VaAndCob/PrintpooP/squareline/assets/puppy/stage0.png

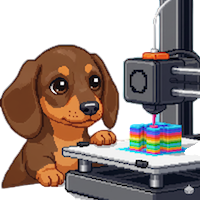
squareline/assets/puppy/stage0.png
