VaAndCob/PrintpooP/squareline/assets/puppy/stage1.png

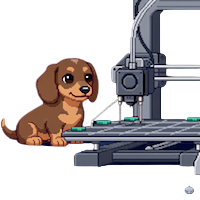
squareline/assets/puppy/stage1.png
