VaAndCob/PrintpooP/squareline/assets/puppy/stage2.png

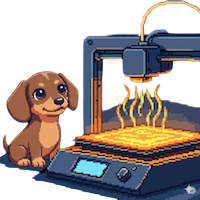
squareline/assets/puppy/stage2.png
