VaAndCob/PrintpooP/squareline/assets/puppy/stage4.png

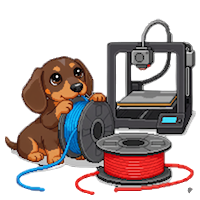
squareline/assets/puppy/stage4.png
