VaAndCob/PrintpooP/squareline/assets/puppy/stage8.png

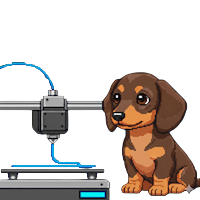
squareline/assets/puppy/stage8.png
