VaAndCob/PrintpooP/squareline/assets/puppy/stage13.png

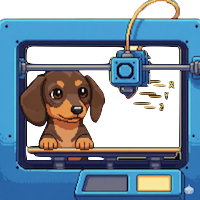
squareline/assets/puppy/stage13.png
