VaAndCob/PrintpooP/squareline/assets/puppy/stage24.png

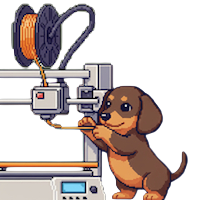
squareline/assets/puppy/stage24.png
