VaAndCob/PrintpooP/squareline/assets/puppy/stage_1.png

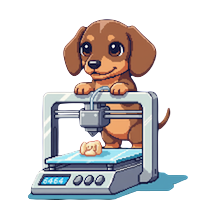
squareline/assets/puppy/stage_1.png
