VaAndCob/PrintpooP/3dprint/printpoop1.jpg

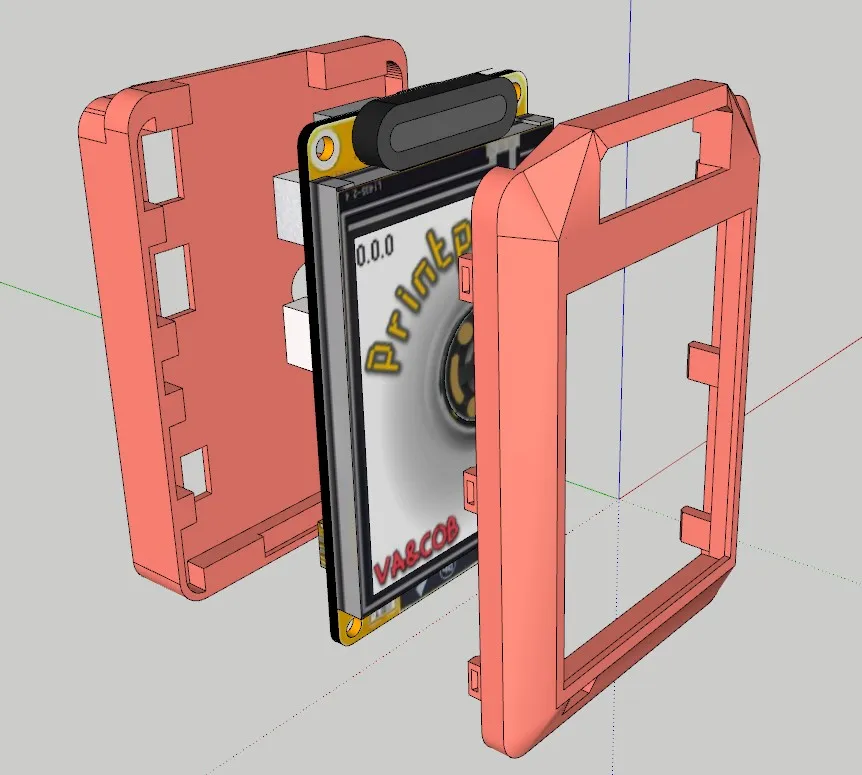
3dprint/printpoop1.jpg
