VaAndCob/PrintpooP/3dprint/printpoop2.jpg

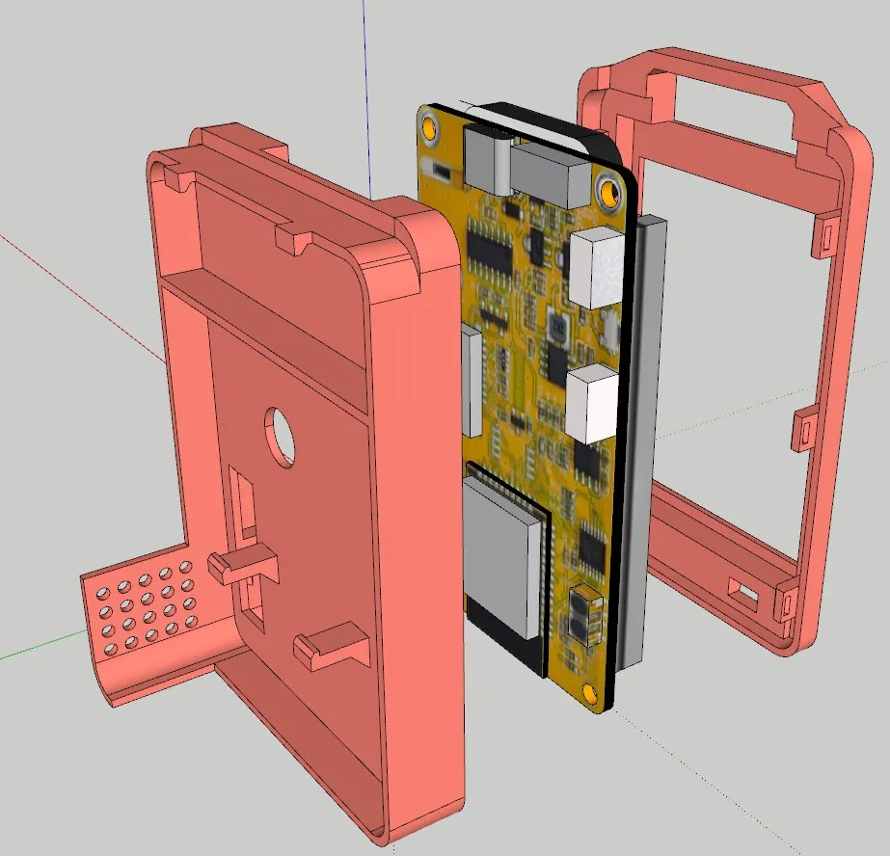
3dprint/printpoop2.jpg
