VaAndCob/PrintpooP/3dprint/printpoop3.jpg

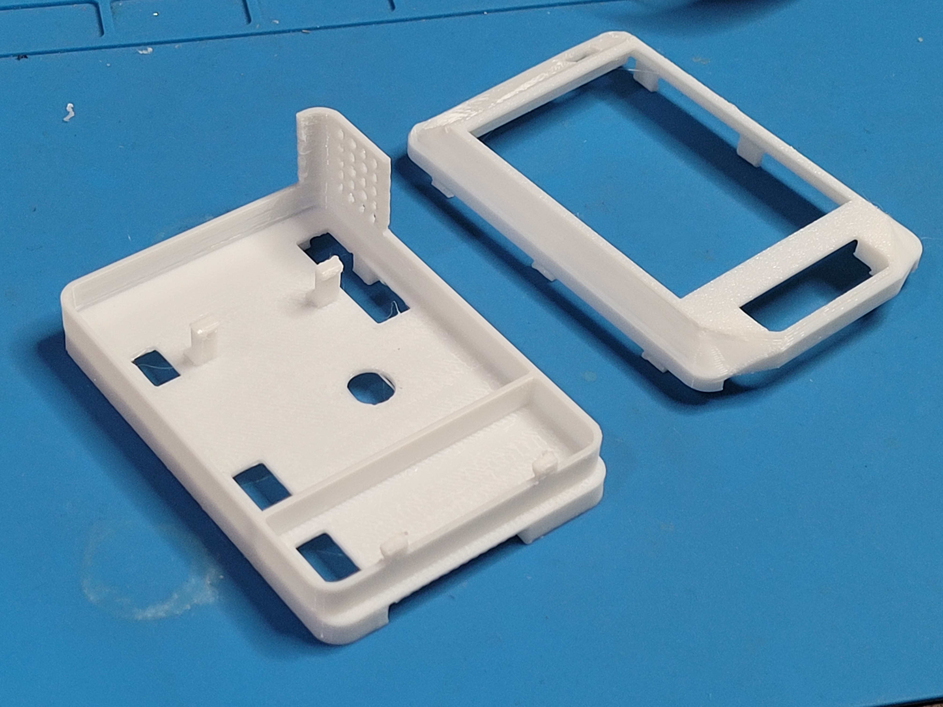
3dprint/printpoop3.jpg
