VaAndCob/PrintpooP/sketch/src/accessory.h

#pragma once

#include <Arduino.h>
#include "LGFX_CYD.h"

#include <SPI.h>
#include <FS.h>
#include <SD.h>
#define SD_MOSI 23
#define SD_MISO 19
#define SD_SCK 18
#define SD_CS 5

extern LGFX tft; /* LGFX instance */
extern SPIClass sd_hspi;  // Using HSPI_HOST, as VSPI is often used by displays.

extern bool print_started;
extern bool print_swing_now;
extern String TZoffset;  // timezone offset
extern String current_version;
extern bool firmware_checked;
extern String firmware_manifest;
extern bool mpu_install;
extern bool flip;
extern uint8_t rotation;
extern bool auto_dim;
extern uint8_t brightness;



void initRTC();
String get_current_time();
/*------------ SOUND EFFECT ----------*/
 void initSpeaker();
 void beepbeep();
 void beep();
 void clickSound();
 /*-----------------------------*/
void autoDim();
void init_TFT_BL(uint8_t BL_PIN);
 /*-----------------------------*/
void setVersion(const String ver, String manifest);
bool newFirmwareAvailable();
/*-----------------------------*/
void mpu_init(byte sda,byte scl);
void print_animation();
void initSDCard();
